McColson/Stompbox-G5/Simulation/g5_stompbox.asc

C1: cap; 250p
C2: cap; 100n
C3: cap; 47n
C4: cap; 22µ
C5: cap; 22µF
C6: cap; 22n
C7: cap; 470pF
C13: cap; 100µ; V=500V Rser=2
C14: cap; 22µ; Rser=2
C15: cap; 22µ; Rser=2
C16: cap; 10µ; Rser=2
I1: current; 100mA
I2: current; 10mA
L1: ind; 7; Rser=100
L2: ind2; 1100
L3: ind2; 1100
L4: ind2; 1
R1: res; 1000k
R2: res; 33k
R3: res; 120k
R4: res; 1k8
R5: res; 50k
R6: res; 100k
R7: res; 1k8
R8: res; 15k
R10: res; 470k
R11: res; 180R
R12: res; 470k
R13: res; 100k
R14: res; 1k
R21: res; 220k
R23: res; 470k
R24: res; 1k
R25: res; 22k
R26: res; 10k
U1: triode; NH12AX7
U2: triode; NH12AX7
U3: triode; NH12AX7
U4: triode; NH12AX7
U6: potentiometer_standard; Rtot=250K wiper=0.5; ""
U7: potentiometer_standard; Rtot=250k wiper=0.5; Rtap=25k tap=0.5
U8: potentiometer_standard; Rtot=100k wiper=0.5; Rtap=10k tap=0.5
U9: potentiometer_standard; Rtot=1000k wiper=0.7; Rtap=250k tap=0.5
U10: potentiometer_standard; Rtot=1K wiper=1; Rtap=150R tap=0.5
V1: voltage; 230
V2: voltage; 320
V3: voltage; SINE(0 1 1K); AC 1. 0
V4: voltage; 235
Named nets: C, 0, B, sin, OUTPUT
.lib potentiometer_standard.lib
.include dmtriodep.inc
.tran 0 15ms 10ms 1ms
;ac oct 1000 20 25000
K1 L2 L3 L4 1
